Daniel-Abdi/Matter-CO2-AirQuality-Sensor/main/relative-humidity-sensor-manager.h

#include <app-common/zap-generated/attributes/Accessors.h>
#include <protocols/interaction_model/StatusCode.h>

#pragma once

namespace chip {
namespace app {
namespace Clusters {

class RelativeHumiditySensorManager
{
public:
    RelativeHumiditySensorManager(EndpointId aEndpointId) : mEndpointId(aEndpointId)
    {
        Protocols::InteractionModel::Status status = RelativeHumidityMeasurement::Attributes::MinMeasuredValue::Set(mEndpointId, 0);
        VerifyOrReturn(Protocols::InteractionModel::Status::Success == status,
                       ChipLogError(NotSpecified, "Failed to set RelativeHumidityMeasurement MinMeasuredValue attribute"));

        status = RelativeHumidityMeasurement::Attributes::MaxMeasuredValue::Set(mEndpointId, 100);
        VerifyOrReturn(Protocols::InteractionModel::Status::Success == status,
                       ChipLogError(NotSpecified, "Failed to set RelativeHumidityMeasurement MaxMeasuredValue attribute"));
    };

    void OnHumidityChangeHandler(uint16_t newValue)
    {
        Protocols::InteractionModel::Status status =
            RelativeHumidityMeasurement::Attributes::MeasuredValue::Set(mEndpointId, newValue);
        VerifyOrReturn(Protocols::InteractionModel::Status::Success == status,
                       ChipLogError(NotSpecified, "Failed to set RelativeHumidityMeasurement MeasuredValue attribute"));
        ChipLogDetail(NotSpecified, "The new RelativeHumidityMeasurement value: %d", newValue);
    }

private:
    EndpointId mEndpointId;
};

} // namespace Clusters
} // namespace app
} // namespace chip
